Bmiga-1200/b1200-hardware/DP_USB2_KVM.kicad_sch

## KiCad design DP_USB2_KVM.kicad_sch (2026-01-02, an earlier design)

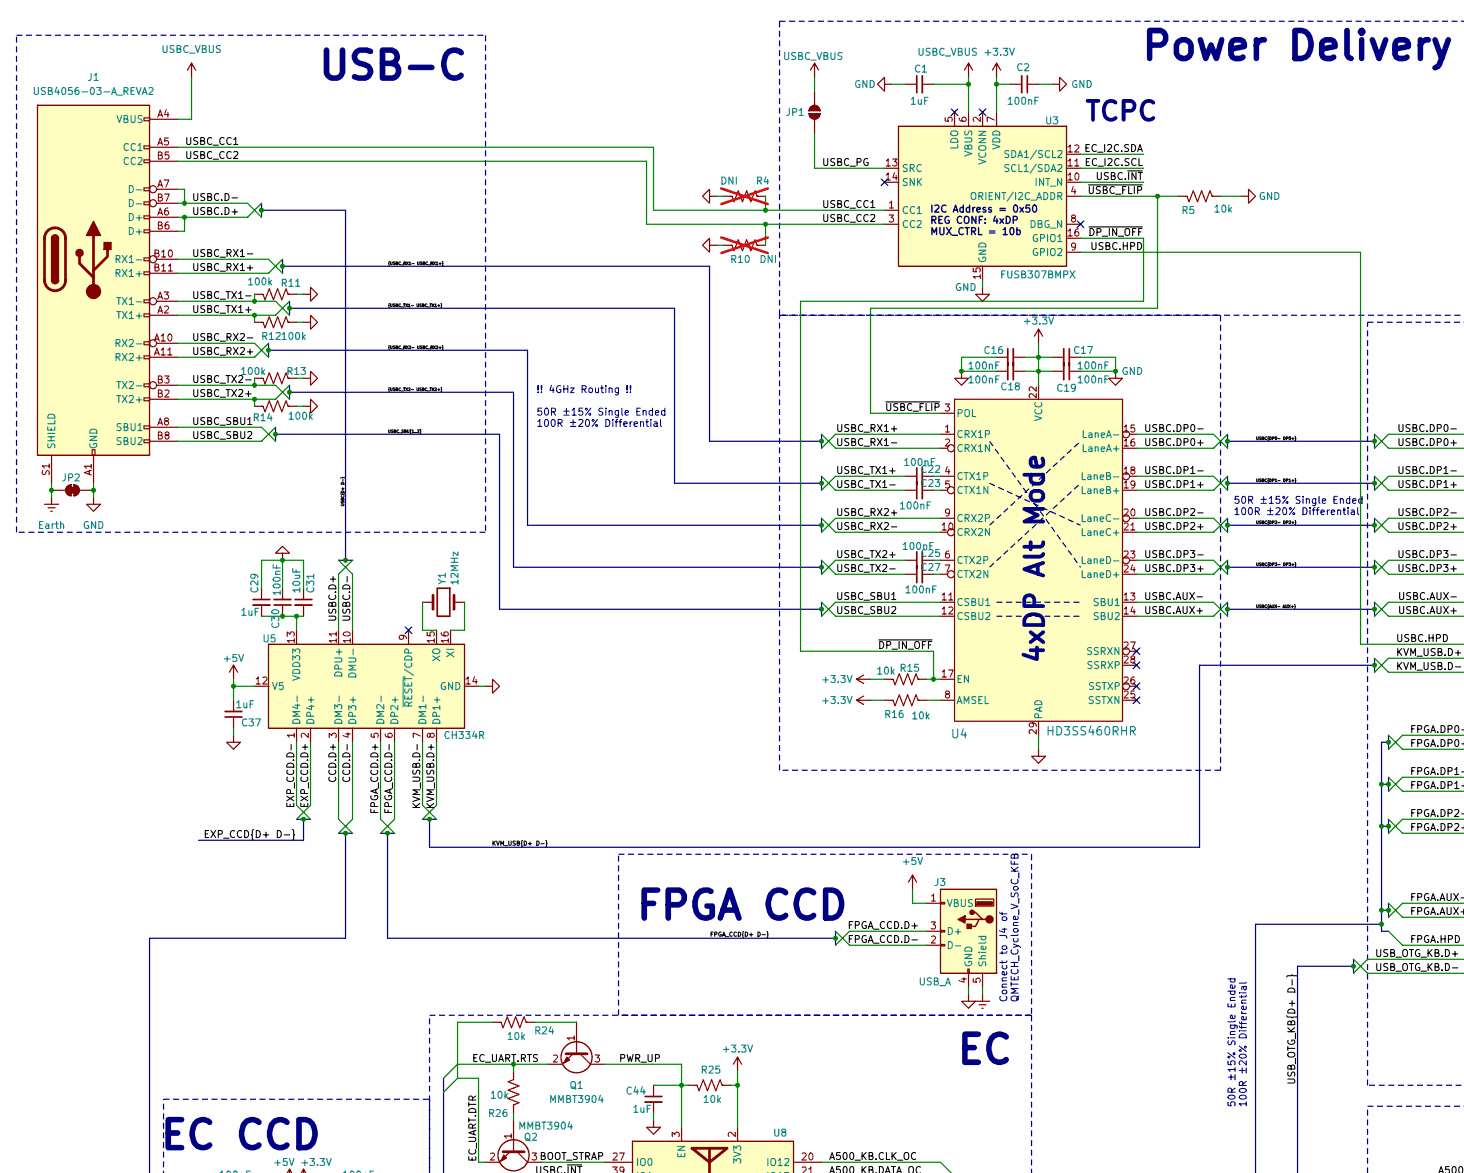
[picture p4: schematic DP_USB2_KVM.kicad_sch, part in row 1, column 1]

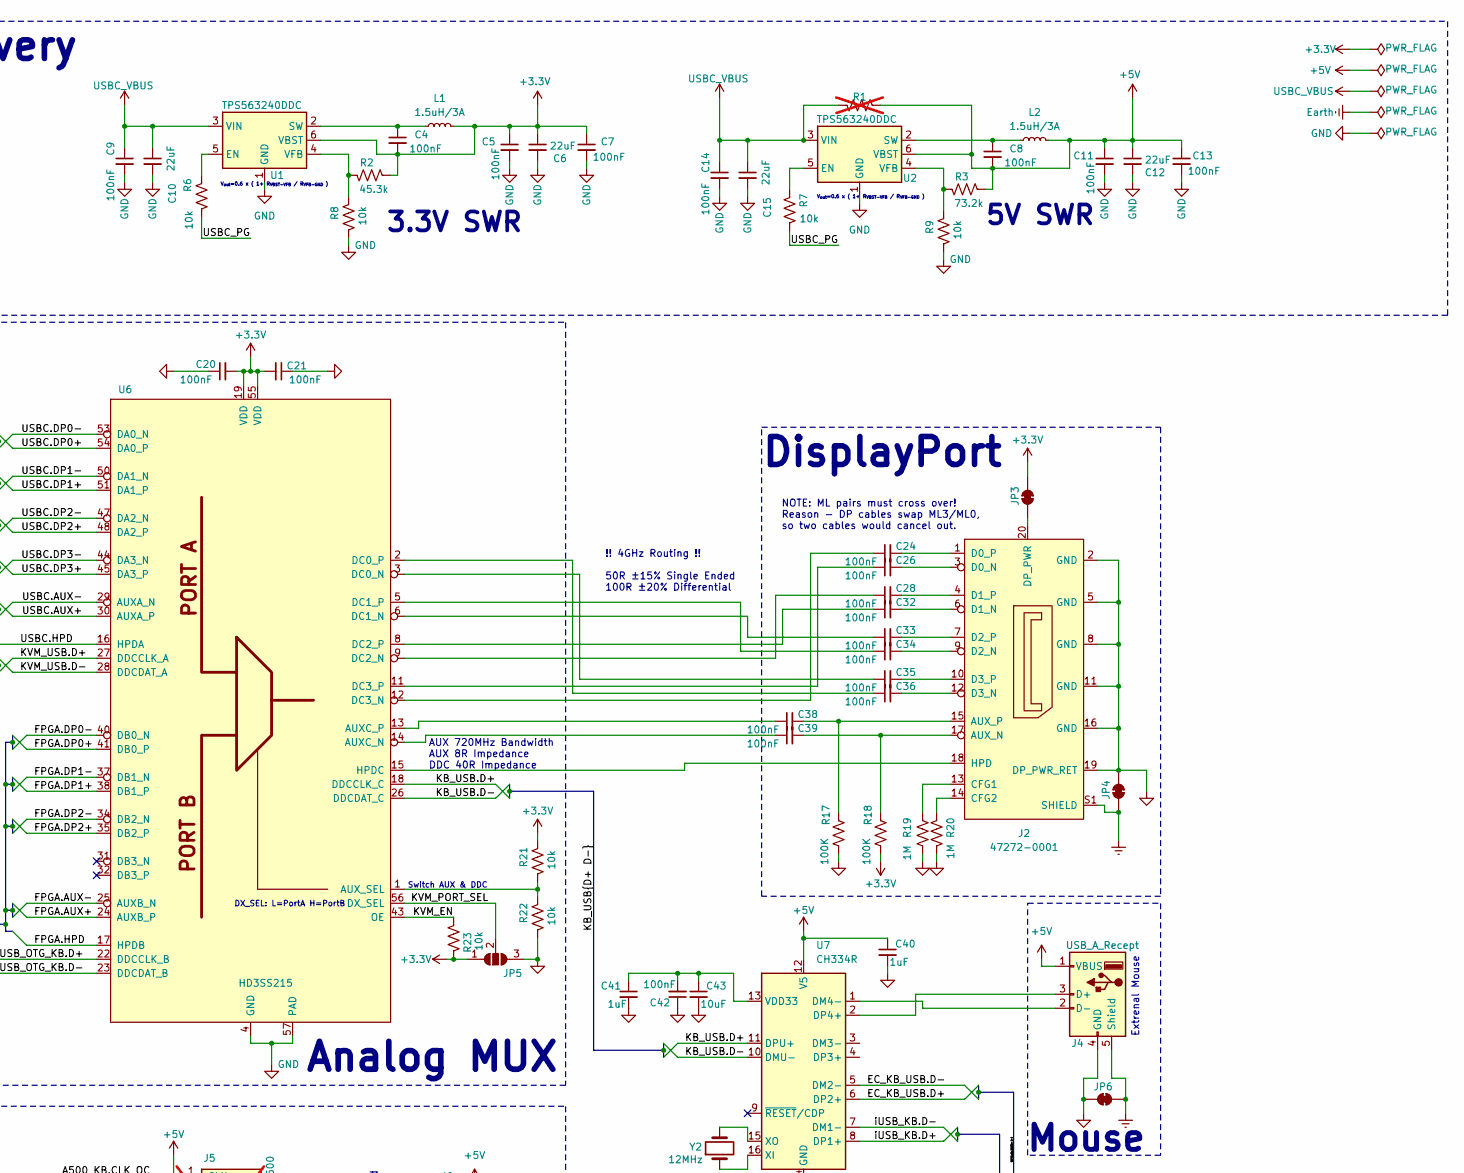
[picture p5: schematic DP_USB2_KVM.kicad_sch, part in row 1, column 2]

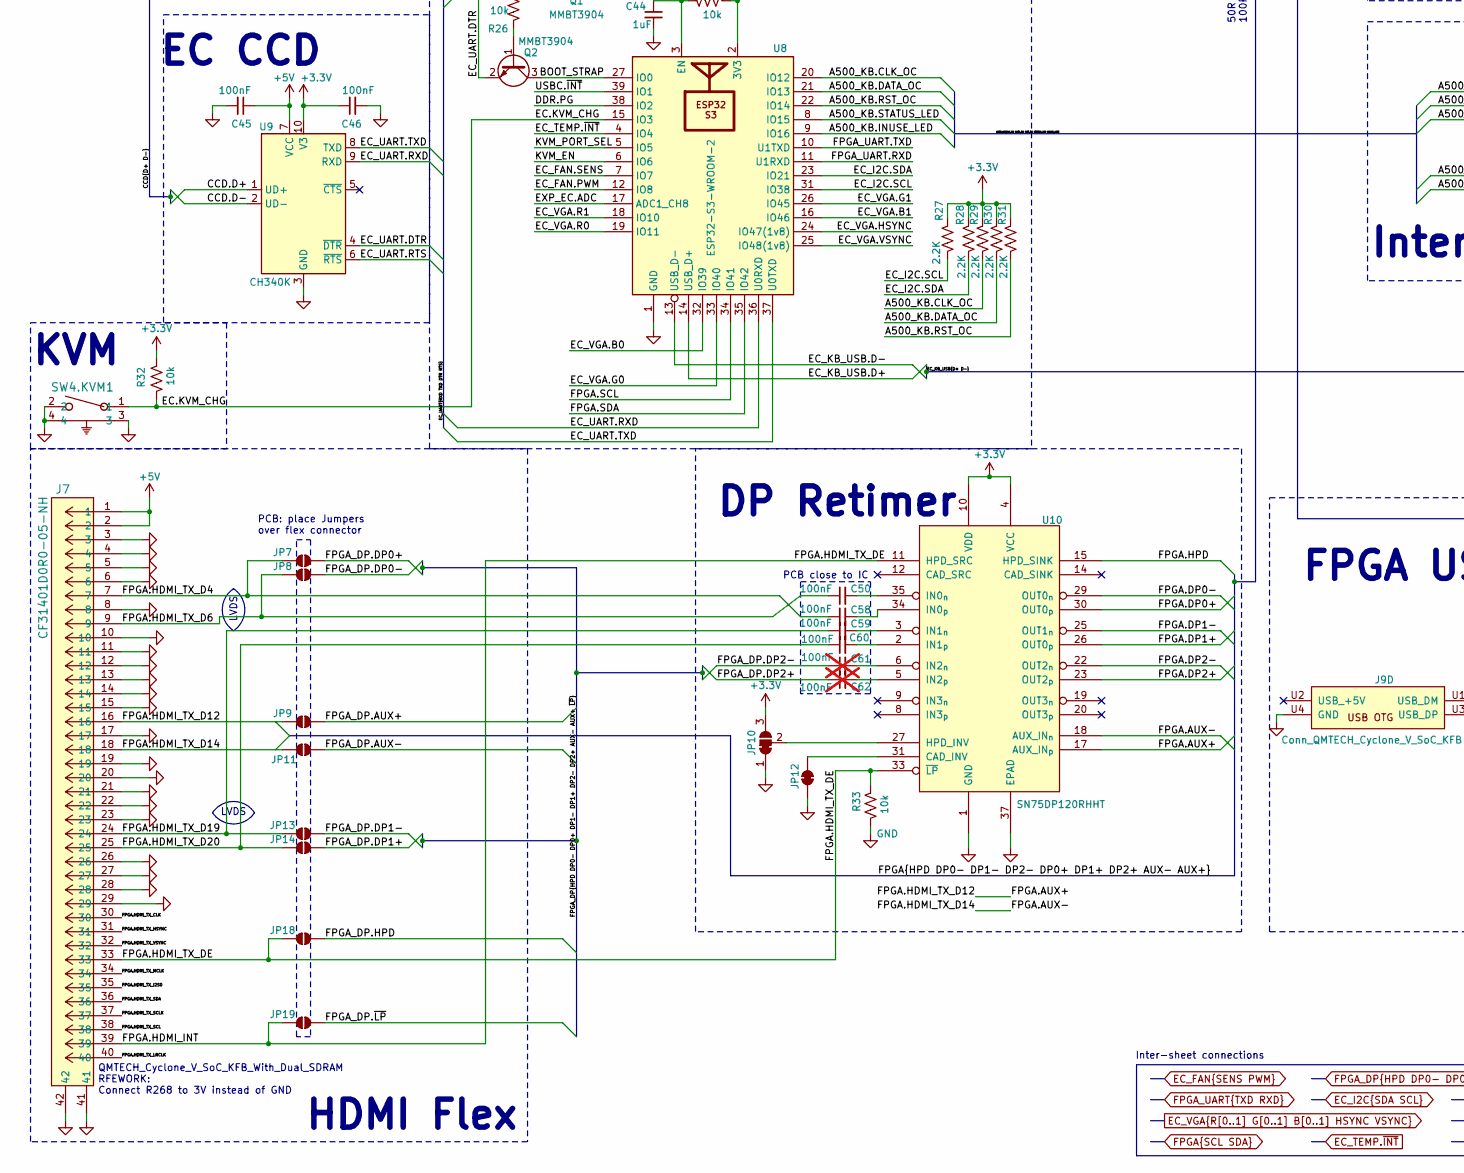
[picture p6: schematic DP_USB2_KVM.kicad_sch, part in row 2, column 1]

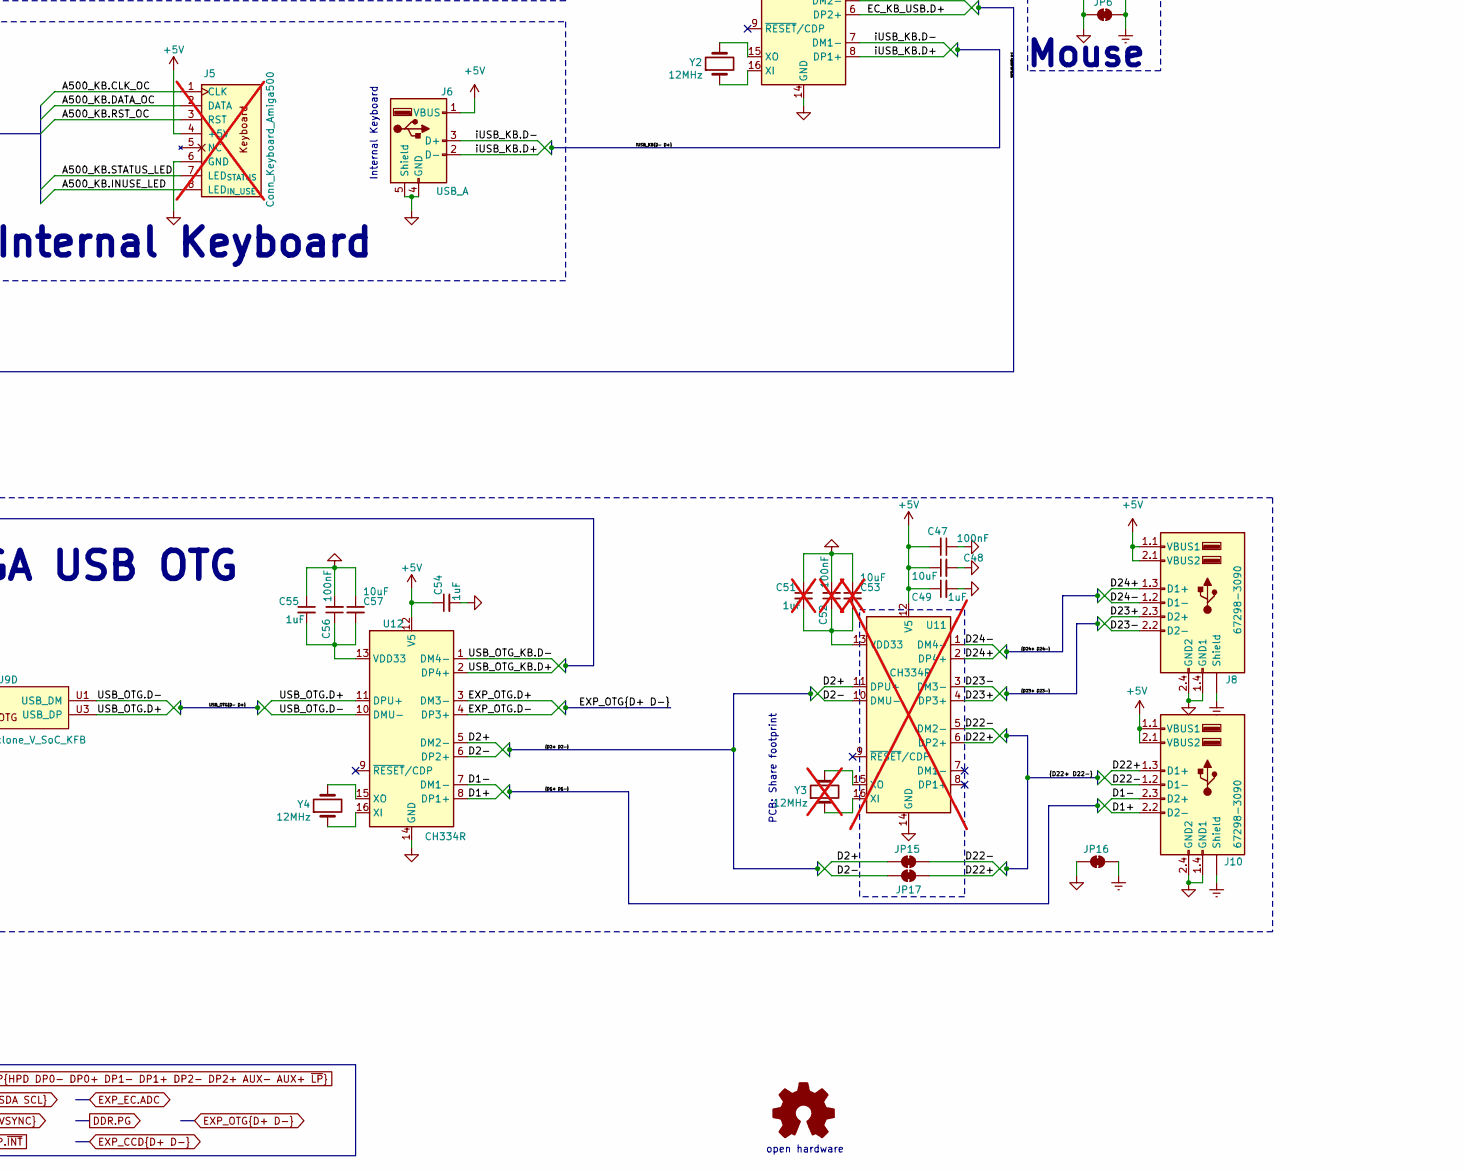
[picture p7: schematic DP_USB2_KVM.kicad_sch, part in row 2, column 2]

Parts:
C1: 1uF; C_0603_1608Metric_Pad1.08x0.95mm_HandSolder
C2, C4, C5, C8, C9, C11, C14, C16, C17, C18, C19, C20, C21, C22, C23, C24, C25, C26, C27, C28, C32, C33, C34, C35, C36, C38, C39, C50, C58, C59, C60: 100nF; C_0603_1608Metric_Pad1.08x0.95mm_HandSolder
C6, C10, C12, C15: 22uF; C_0603_1608Metric_Pad1.08x0.95mm_HandSolder
C7, C13: 100nF; C_1210_3225Metric_Pad1.33x2.70mm_HandSolder
C29, C37, C40, C41, C44, C49, C54, C55: 1uF; C_0805_2012Metric_Pad1.18x1.45mm_HandSolder
C30, C42, C45, C46, C47, C56: 100nF; C_0805_2012Metric_Pad1.18x1.45mm_HandSolder
C31, C43, C48, C57: 10uF; C_0805_2012Metric_Pad1.18x1.45mm_HandSolder
C51: 1uF; C_0805_2012Metric_Pad1.18x1.45mm_HandSolder; not fitted
C52: 100nF; C_0805_2012Metric_Pad1.18x1.45mm_HandSolder; not fitted
C53: 10uF; C_0805_2012Metric_Pad1.18x1.45mm_HandSolder; not fitted
C61, C62: 100nF; C_0603_1608Metric_Pad1.08x0.95mm_HandSolder; not fitted
J1: USB4056-03-A_REVA2; GCT_USB4056-03-A_REVA2; PARTREV A2
J2: 47272-0001; MOLEX_47272-0001
J3, J6: USB_A; USB_A_Molex_105057_Vertical
J4: USB_A_Recept; USB_A_Molex_67643_Horizontal
J5: Conn_Keyboard_Amiga500; PinHeader_1x08_P2.54mm_Vertical; not fitted
J7: CF31401D0R0-05-NH; CONN40_CF3140_CVI
J8, J10: 67298-3090; USB_MOLEX_8PIN_RA
J9: Conn_QMTECH_Cyclone_V_SoC_KFB; PinSocket_QMTECH_Cyclone_V_KFN_2x20_P2.54mm_Vertical
JP1, JP7, JP8, JP9, JP11, JP13, JP14, JP18, JP19: SolderJumper_2_Open; SolderJumper-2_P1.3mm_Open_Pad1.0x1.5mm
JP2, JP3, JP4, JP6, JP12, JP15, JP16, JP17: SolderJumper_2_Bridged; SolderJumper-2_P1.3mm_Bridged_Pad1.0x1.5mm
JP5: SolderJumper_3_Open; SolderJumper-3_P1.3mm_Open_Pad1.0x1.5mm
JP10: SolderJumper_3_Bridged12; SolderJumper-3_P1.3mm_Bridged12_Pad1.0x1.5mm
L1, L2: 1.5uH/3A; L_1008_2520Metric_Pad1.43x2.20mm_HandSolder
Q1, Q2: MMBT3904; SOT-23_Handsoldering
R1, R4, R10: DNI; R_0603_1608Metric_Pad0.98x0.95mm_HandSolder; not fitted
R2: 45.3k; R_0603_1608Metric_Pad0.98x0.95mm_HandSolder
R3: 73.2k; R_0603_1608Metric_Pad0.98x0.95mm_HandSolder
R5, R6, R7, R8, R9, R15, R16, R21, R22, R23, R24, R25, R26, R32, R33: 10k; R_0603_1608Metric_Pad0.98x0.95mm_HandSolder
R11, R12, R13, R14: 100k; R_0603_1608Metric_Pad0.98x0.95mm_HandSolder
R17, R18: 100K; R_0603_1608Metric_Pad0.98x0.95mm_HandSolder
R19, R20: 1M; R_0603_1608Metric_Pad0.98x0.95mm_HandSolder
R27, R28, R29, R30, R31: 2.2K; R_0603_1608Metric_Pad0.98x0.95mm_HandSolder
SW4.KVM1: 1-1825027-1; SW2_1825027-A_TEC
U1, U2: TPS563240DDC; SOT-23-6_Handsoldering
U3: FUSB307BMPX; WQFN-16-1EP_3x3mm_P0.5mm_EP1.75x1.75mm_ThermalVias
U4: HD3SS460RHR; RHR0028A
U5, U7, U12: CH334R; QSOP-16_3.9x4.9mm_P0.635mm
U6: HD3SS215; VQFN-56_EP_7.8x7.8_Pitch0.5mm
U8: ESP32-S3-WROOM-2
U9: CH340K; SSOP-10-1EP_3.9x4.9mm_P1mm_EP2.1x3.3mm
U10: SN75DP120RHHT; QFN50P600X600X100-37N; MPN SN75DP120RHHT
U11: CH334R; QSOP-16_3.9x4.9mm_P0.635mm; not fitted
Y1, Y2, Y4: 12MHz; Crystal_HC49-U_Horizontal
Y3: 12MHz; Crystal_HC49-U_Horizontal; not fitted

Connections:
+3.3V: C2.2, C4.2, C5.1, C6.1, C7.1, C16.2, C17.2, C18.2, C19.2, C20.2, C21.2, C46.1, JP3.1 (A), JP5.1 (A), JP10.3 (B), L1.2, R2.1, R15.2, R16.2, R18.2, R21.2, R23.2, R25.1, R27.2, R28.2, R29.2, R30.2, R31.2, R32.1, U1.6 (VBST), U3.7 (VDD), U4.22 (VCC), U6.19 (VDD), U6.55 (VDD), U8.2 (3V3), U9.10 (V3), U10.4 (VCC), U10.10 (VDD), U10.16 (VCC), U10.24 (VCC), U10.28 (VCC), U10.36 (VCC)
+5V: C8.2, C11.1, C12.1, C13.1, C37.2, C40.1, C45.1, C47.2, C48.1, C49.1, C54.1, J3.1 (VBUS), J4.1 (VBUS), J5.4 (+5V), J6.1 (VBUS), J7.1, J7.2, J8.1.1 (VBUS1), J8.2.1 (VBUS2), J10.1.1 (VBUS1), J10.2.1 (VBUS2), L2.2, R1.1, R3.1, U2.6 (VBST), U5.12 (V5), U7.12 (V5), U9.7 (VCC), U11.12 (V5), U12.12 (V5)
A500_KB.CLK_OC: J5.1 (CLK), R29.1, U8.20 (IO12)
A500_KB.DATA_OC: J5.2 (DATA), R30.1, U8.21 (IO13)
A500_KB.INUSE_LED: J5.8 (LED_{IN_USE}), U8.9 (IO16)
A500_KB.RST_OC: J5.3 (RST), R31.1, U8.22 (IO14)
A500_KB.STATUS_LED: J5.7 (LED_{STATUS}), U8.8 (IO15)
BOOT_STRAP: Q2.3 (C), U8.27 (IO0)
CCD.D+: U5.3 (DM3-), U9.1 (UD+)
CCD.D-: U5.4 (DP3+), U9.2 (UD-)
D1+: J10.2.2 (D2-), U12.8 (DP1+)
D1-: J10.2.3 (D2+), U12.7 (DM1-)
D2+: JP15.1 (A), U11.11 (DPU+), U12.5 (DM2-)
D2-: JP17.1 (A), U11.10 (DMU-), U12.6 (DP2+)
D22+: J10.1.3 (D1+), JP17.2 (B), U11.6 (DP2+)
D22-: J10.1.2 (D1-), JP15.2 (B), U11.5 (DM2-)
D23+: J8.2.3 (D2+), U11.4 (DP3+)
D23-: J8.2.2 (D2-), U11.3 (DM3-)
D24+: J8.1.3 (D1+), U11.2 (DP4+)
D24-: J8.1.2 (D1-), U11.1 (DM4-)
DDR.PG: U8.38 (IO2)
EC.KVM_CHG: R32.2, SW4.KVM1.1, U8.15 (IO3)
EC_FAN.PWM: U8.12 (IO8)
EC_FAN.SENS: U8.7 (IO7)
EC_I2C.SCL: R27.1, U3.11 (SCL1/SDA2), U8.31 (IO38)
EC_I2C.SDA: R28.1, U3.12 (SDA1/SCL2), U8.23 (IO21)
EC_KB_USB.D+: U7.6 (DP2+), U8.14 (USB_D+)
EC_KB_USB.D-: U7.5 (DM2-), U8.13 (USB_D-)
EC_TEMP.~INT: U8.4 (IO4)
EC_UART.DTR: Q1.2 (E), Q2.2 (E), R24.2, R26.2, U9.4 (~DTR), U9.6 (~RTS)
EC_UART.RXD: U8.36 (U0RXD), U9.9 (RXD)
EC_UART.TXD: U8.37 (U0TXD), U9.8 (TXD)
EC_VGA.B0: U8.32 (MTCK)
EC_VGA.B1: U8.16 (IO46)
EC_VGA.G0: U8.33 (MTDO)
EC_VGA.G1: U8.26 (IO45)
EC_VGA.HSYNC: U8.24 (IO47(1v8))
EC_VGA.R0: U8.19 (IO11)
EC_VGA.R1: U8.18 (IO10)
EC_VGA.VSYNC: U8.25 (IO48(1v8))
EXP_CCD.D+: U5.2 (DP4+)
EXP_CCD.D-: U5.1 (DM4-)
EXP_EC.ADC: U8.17 (IO9)
EXP_OTG.D+: U12.3 (DM3-)
EXP_OTG.D-: U12.4 (DP3+)
Earth: J1.S1 (SHIELD), J1.S2 (SHIELD), J1.S3 (SHIELD), J1.S4 (SHIELD), J2.S1 (SHIELD), J2.S2 (SHIELD), J2.S3 (SHIELD), J2.S4 (SHIELD), J3.5 (Shield), J4.5 (Shield), J8.GND@3 (Shield), J8.GND@4 (Shield), J8.GND@5 (Shield), J8.GND@6 (Shield), J10.GND@3 (Shield), J10.GND@4 (Shield), J10.GND@5 (Shield), J10.GND@6 (Shield), JP2.1 (A), JP4.2 (B), JP6.2 (B), JP16.2 (B)
FPGA.AUX+: J7.16, JP9.2 (B), U6.24 (AUXB_P), U10.17 (AUX_IN_{p})
FPGA.AUX-: J7.18, JP11.2 (B), U6.25 (AUXB_N), U10.18 (AUX_IN_{n})
FPGA.DP0+: U6.41 (DB0_P), U10.30 (OUT0_{p})
FPGA.DP0-: U6.40 (DB0_N), U10.29 (OUT0_{n})
FPGA.DP1+: U6.38 (DB1_P), U10.26 (OUT0_{p})
FPGA.DP1-: U6.37 (DB1_N), U10.25 (OUT1_{n})
FPGA.DP2+: U6.35 (DB2_P), U10.23 (OUT2_{p})
FPGA.DP2-: U6.34 (DB2_N), U10.22 (OUT2_{n})
FPGA.HDMI_INT: J7.33, J7.39, JP18.2 (B), JP19.2 (B), R33.2, U10.11 (HPD_SRC), U10.33 (~LP)
FPGA.HDMI_TX_CLK: J7.30
FPGA.HDMI_TX_D4: C58.1, J7.7, JP7.2 (B)
FPGA.HDMI_TX_D6: C50.1, J7.9, JP8.2 (B)
FPGA.HDMI_TX_D19: C59.1, J7.24, JP13.2 (B)
FPGA.HDMI_TX_D20: C60.1, J7.25, JP14.2 (B)
FPGA.HDMI_TX_HSYNC: J7.31
FPGA.HDMI_TX_I2S0: J7.35
FPGA.HDMI_TX_LRCLK: J7.40
FPGA.HDMI_TX_MCLK: J7.34
FPGA.HDMI_TX_SCL: J7.38
FPGA.HDMI_TX_SCLK: J7.37
FPGA.HDMI_TX_SDA: J7.36
FPGA.HDMI_TX_VSYNC: J7.32
FPGA.HPD: U6.17 (HPDB), U10.15 (HPD_SINK)
FPGA.SCL: U8.34 (MTDI)
FPGA.SDA: U8.35 (MTMS)
FPGA_CCD.D+: J3.3 (D+), U5.5 (DM2-)
FPGA_CCD.D-: J3.2 (D-), U5.6 (DP2+)
FPGA_DP.AUX+: JP9.1 (A)
FPGA_DP.AUX-: JP11.1 (A)
FPGA_DP.DP0+: JP7.1 (A)
FPGA_DP.DP0-: JP8.1 (A)
FPGA_DP.DP1+: JP14.1 (A)
FPGA_DP.DP1-: JP13.1 (A)
FPGA_DP.DP2+: C62.1
FPGA_DP.DP2-: C61.1
FPGA_DP.HPD: JP18.1 (A)
FPGA_DP.~LP: JP19.1 (A)
FPGA_UART.RXD: U8.11 (IO18)
FPGA_UART.TXD: U8.10 (IO17)
GND: C1.1, C2.1, C5.2, C6.2, C7.2, C9.2, C10.2, C11.2, C12.2, C13.2, C14.2, C15.2, C16.1, C17.1, C18.1, C19.1, C20.1, C21.1, C29.1, C30.2, C31.1, C37.1, C40.2, C41.2, C42.1, C43.2, C44.2, C45.2, C46.2, C47.1, C48.2, C49.2, C51.1, C52.2, C53.1, C54.2, C55.1, C56.2, C57.1, J1.A1 (GND), J1.A12 (GND), J1.B1 (GND), J1.B12 (GND), J2.2 (GND), J2.5 (GND), J2.8 (GND), J2.11 (GND), J2.16 (GND), J2.19 (DP_PWR_RET), J3.4 (GND), J4.4 (GND), J5.6 (GND), J6.4 (GND), J6.5 (Shield), J7.3, J7.4, J7.5, J7.6, J7.8, J7.10, J7.11, J7.12, J7.13, J7.14, J7.15, J7.17, J7.19, J7.20, J7.21, J7.22, J7.23, J7.26, J7.27, J7.28, J7.29, J7.41, J7.42, J8.1.4 (GND1), J8.2.4 (GND2), J9.U4 (GND), J10.1.4 (GND1), J10.2.4 (GND2), JP2.2 (B), JP4.1 (A), JP5.3 (B), JP6.1 (A), JP10.1 (A), JP12.2 (B), JP16.1 (A), R4.1, R5.1, R8.1, R9.1, R10.1, R11.2, R12.2, R13.2, R14.2, R17.2, R19.2, R20.2, R22.1, R33.1, SW4.KVM1.2, SW4.KVM1.3, SW4.KVM1.4, U1.1 (GND), U2.1 (GND), U3.15 (GND), U3.17 (GND), U4.29 (PAD), U5.14 (GND), U6.4 (GND), U6.7 (GND), U6.10 (GND), U6.33 (GND), U6.36 (GND), U6.39 (GND), U6.46 (GND), U6.49 (GND), U6.52 (GND), U6.57 (PAD), U7.14 (GND), U8.1 (GND), U8.40 (GND), U8.41 (GND), U9.3 (GND), U9.11 (GND), U10.1 (GND), U10.7 (GND), U10.13 (GND), U10.21 (GND), U10.32 (GND), U10.37 (EPAD), U11.14 (GND), U12.14 (GND)
KB_USB.D+: U6.18 (DDCCLK_C), U7.11 (DPU+)
KB_USB.D-: U6.26 (DDCDAT_C), U7.10 (DMU-)
KVM_EN: R23.1, U6.43 (OE), U8.6 (IO6)
KVM_PORT_SEL: JP5.2 (C), U6.56 (DX_SEL), U8.5 (IO5)
KVM_USB.D+: U5.8 (DP1+), U6.27 (DDCCLK_A)
KVM_USB.D-: U5.7 (DM1-), U6.28 (DDCDAT_A)
unnamed: C4.1, L1.1, U1.2 (SW)
unnamed: C8.1, L2.1, U2.2 (SW)
unnamed: C22.2, U4.4 (CTX1P)
unnamed: C23.2, U4.5 (CTX1N)
unnamed: C24.1, U6.12 (DC3_N)
unnamed: C24.2, J2.1 (D0_P)
unnamed: C25.2, U4.6 (CTX2P)
unnamed: C26.1, U6.11 (DC3_P)
unnamed: C26.2, J2.3 (D0_N)
unnamed: C27.2, U4.7 (CTX2N)
unnamed: C28.1, U6.9 (DC2_N)
unnamed: C28.2, J2.4 (D1_P)
unnamed: C29.2, C30.1, C31.2, U5.13 (VDD33)
unnamed: C32.1, U6.8 (DC2_P)
unnamed: C32.2, J2.6 (D1_N)
unnamed: C33.1, U6.6 (DC1_N)
unnamed: C33.2, J2.7 (D2_P)
unnamed: C34.1, U6.5 (DC1_P)
unnamed: C34.2, J2.9 (D2_N)
unnamed: C35.1, U6.3 (DC0_N)
unnamed: C35.2, J2.10 (D3_P)
unnamed: C36.1, U6.2 (DC0_P)
unnamed: C36.2, J2.12 (D3_N)
unnamed: C38.1, U6.13 (AUXC_P)
unnamed: C38.2, J2.15 (AUX_P), R17.1
unnamed: C39.1, U6.14 (AUXC_N)
unnamed: C39.2, J2.17 (AUX_N), R18.1
unnamed: C41.1, C42.2, C43.1, U7.13 (VDD33)
unnamed: C50.2, U10.35 (IN0_{n})
unnamed: C51.2, C52.1, C53.2, U11.13 (VDD33)
unnamed: C55.2, C56.1, C57.2, U12.13 (VDD33)
unnamed: C58.2, U10.34 (IN0_{p})
unnamed: C59.2, U10.3 (IN1_{n})
unnamed: C60.2, U10.2 (IN1_{p})
unnamed: C61.2, U10.6 (IN2_{n})
unnamed: C62.2, U10.5 (IN2_{p})
unnamed: J2.13 (CFG1), R19.1
unnamed: J2.14 (CFG2), R20.1
unnamed: J2.18 (HPD), U6.15 (HPDC)
unnamed: J2.20 (DP_PWR), JP3.2 (B)
unnamed: J4.2 (D-), U7.1 (DM4-)
unnamed: J4.3 (D+), U7.2 (DP4+)
unnamed: JP10.2 (C), U10.27 (HPD_INV)
unnamed: JP12.1 (A), U10.31 (CAD_INV)
unnamed: Q1.1 (B), R24.1
unnamed: Q2.1 (B), R26.1
unnamed: R2.2, R8.2, U1.4 (VFB)
unnamed: R3.2, R9.2, U2.4 (VFB)
unnamed: R6.2, U1.5 (EN)
unnamed: R7.2, U2.5 (EN)
unnamed: R16.1, U4.8 (AMSEL)
unnamed: R21.1, R22.2, U6.1 (AUX_SEL)
unnamed: U5.15 (XO), Y1.2
unnamed: U5.16 (XI), Y1.1
unnamed: U7.15 (XO), Y2.2
unnamed: U7.16 (XI), Y2.1
unnamed: U8.28 (NC), U8.29 (NC), U8.30 (NC)
unnamed: U11.15 (XO), Y3.2
unnamed: U11.16 (XI), Y3.1
unnamed: U12.15 (XO), Y4.2
unnamed: U12.16 (XI), Y4.1
PWR_UP: C44.1, Q1.3 (C), R25.2, U8.3 (EN)
USBC.AUX+: U4.14 (SBU2), U6.30 (AUXA_P)
USBC.AUX-: U4.13 (SBU1), U6.29 (AUXA_N)
USBC.D+: J1.A6 (D+), J1.B6 (D+), U5.11 (DPU+)
USBC.D-: J1.A7 (D-), J1.B7 (D-), U5.10 (DMU-)
USBC.DP0+: U4.16 (LaneA+), U6.54 (DA0_P)
USBC.DP0-: U4.15 (LaneA-), U6.53 (DA0_N)
USBC.DP1+: U4.19 (LaneB+), U6.51 (DA1_P)
USBC.DP1-: U4.18 (LaneB-), U6.50 (DA1_N)
USBC.DP2+: U4.21 (LaneC+), U6.48 (DA2_P)
USBC.DP2-: U4.20 (LaneC-), U6.47 (DA2_N)
USBC.DP3+: U4.24 (LaneD+), U6.45 (DA3_P)
USBC.DP3-: U4.23 (LaneD-), U6.44 (DA3_N)
USBC.HPD: R15.1, U3.9 (GPIO2), U3.16 (GPIO1), U4.17 (EN), U6.16 (HPDA)
USBC.~INT: U3.10 (INT_N), U8.39 (IO1)
USBC_CC1: J1.A5 (CC1), R4.2, U3.1 (CC1)
USBC_CC2: J1.B5 (CC2), R10.2, U3.3 (CC2)
USBC_PG: JP1.1 (A), R6.1, R7.1, U3.13 (SRC)
USBC_RX1+: J1.B11 (RX1+), U4.1 (CRX1P)
USBC_RX1-: J1.B10 (RX1-), U4.2 (CRX1N)
USBC_RX2+: J1.A11 (RX2+), U4.9 (CRX2P)
USBC_RX2-: J1.A10 (RX2-), U4.10 (CRX2N)
USBC_SBU1: J1.A8 (SBU1), U4.11 (CSBU1)
USBC_SBU2: J1.B8 (SBU2), U4.12 (CSBU2)
USBC_TX1+: C22.1, J1.A2 (TX1+), R12.1
USBC_TX1-: C23.1, J1.A3 (TX1-), R11.1
USBC_TX2+: C25.1, J1.B2 (TX2+), R14.1
USBC_TX2-: C27.1, J1.B3 (TX2-), R13.1
USBC_VBUS: C1.2, C9.1, C10.1, C14.1, C15.1, J1.A4 (VBUS), J1.A9 (VBUS), J1.B4 (VBUS), J1.B9 (VBUS), JP1.2 (B), R1.2, U1.3 (VIN), U2.3 (VIN), U3.6 (VBUS)
USB_OTG.D+: J9.U3 (USB_DP), U12.11 (DPU+)
USB_OTG.D-: J9.U1 (USB_DM), U12.10 (DMU-)
USB_OTG_KB.D+: U6.22 (DDCCLK_B), U12.2 (DP4+)
USB_OTG_KB.D-: U6.23 (DDCDAT_B), U12.1 (DM4-)
iUSB_KB.D+: J6.2 (D-), U7.8 (DP1+)
iUSB_KB.D-: J6.3 (D+), U7.7 (DM1-)
~USBC_FLIP: R5.2, U3.4 (ORIENT/I2C_ADDR), U4.3 (POL)

Notes on the sheet:
PCB: Share footprint
AUX 720MHz Bandwidth AUX 8R Impedance DDC 40R Impedance
5V SWR
I2C Address = 0x50 REG CONF: 4xDP MUX_CTRL = 10b
50R ±15% Single Ended 100R ±20% Differential
LVDS
3.3V SWR
V_{out}=0.6 x ( 1+ R_{VBST-VFB} / R_{VFB-GND} )
PCB: place Jumpers over flex connector
USB-C
Extrenal Mouse
FPGA USB OTG
FPGA CCD
4xDP Alt Mode
Inter-sheet connections
Connect to J4 of QMTECH_Cyclone_V_SoC_KFB
open hardware
Mouse
TCPC
EC CCD
!! 4GHz Routing !! 50R ±15% Single Ended 100R ±20% Differential
NOTE: ML pairs must cross over! Reason - DP cables swap ML3/ML0, so two cables would cancel out.
Internal Keyboard
QMTECH_Cyclone_V_SoC_KFB_With_Dual_SDRAM RFEWORK: Connect R268 to 3V instead of GND
DisplayPort
Analog MUX
Switch AUX & DDC
HDMI Flex
Power Delivery
KVM
PCB close to IC
DP Retimer
DX_SEL: L=PortA H=PortB
