Bmiga-1200/b1200-hardware/fpga_usb_hub.kicad_sch

## KiCad design fpga_usb_hub.kicad_sch (2026-07-11, an earlier design)

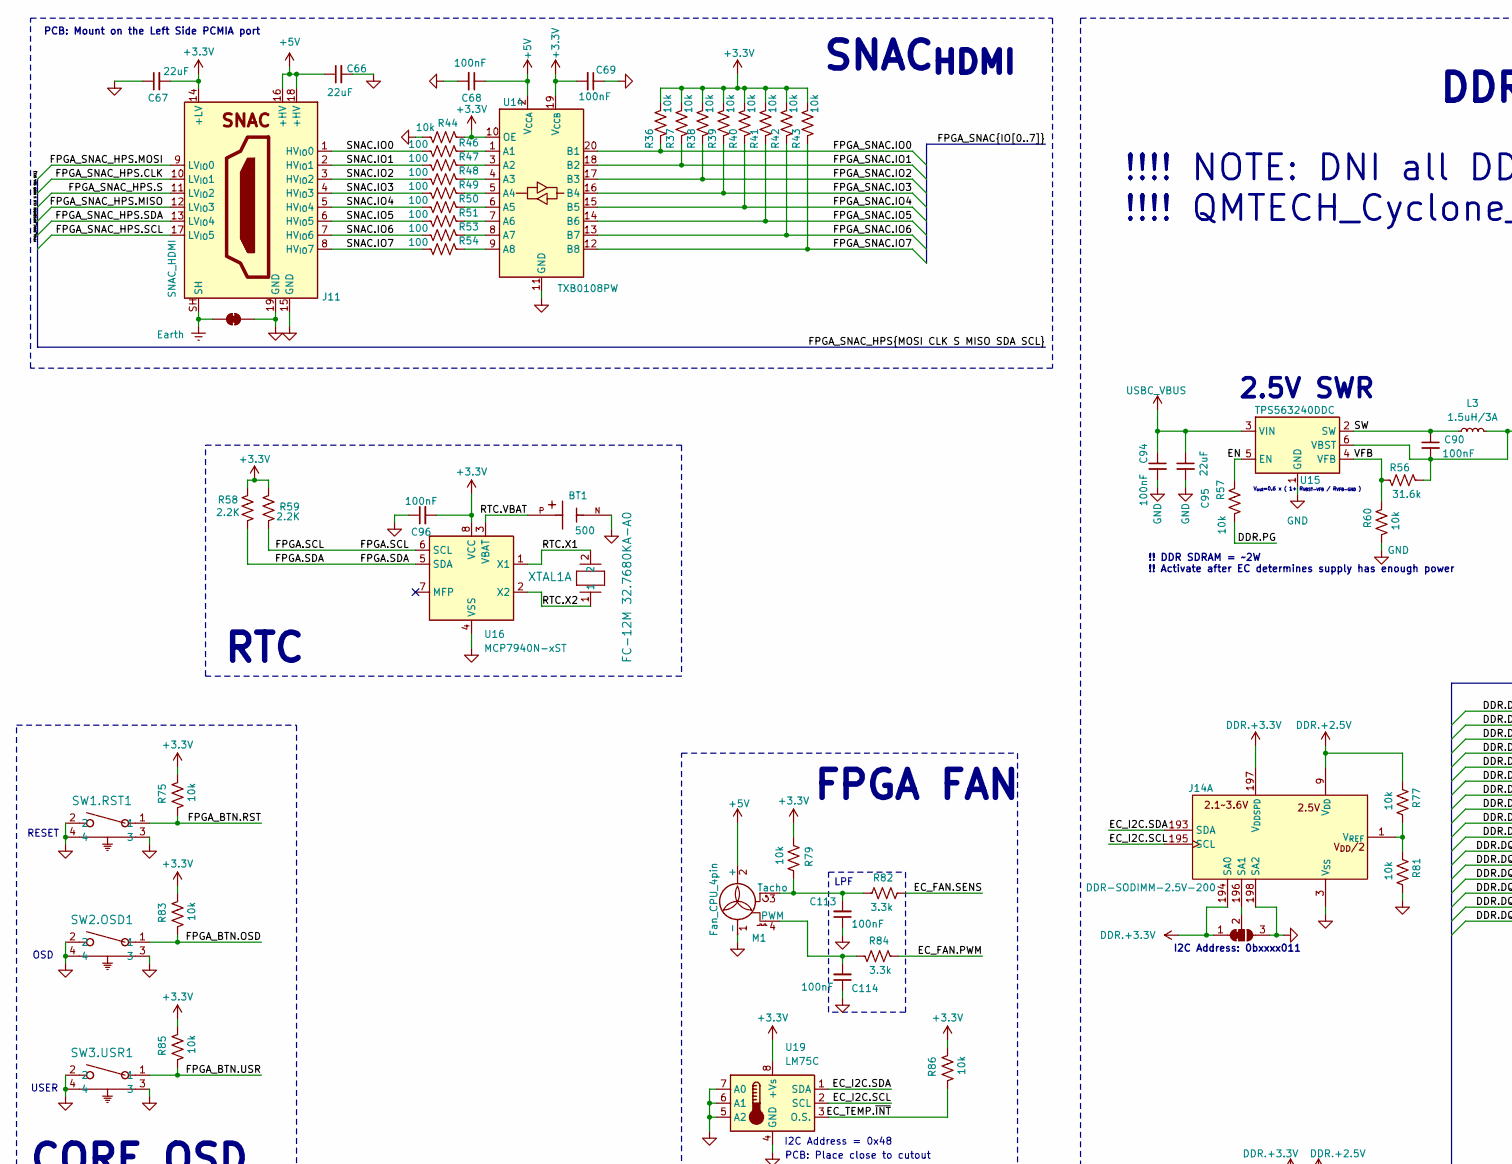
[picture p8: schematic fpga_usb_hub.kicad_sch, part in row 1, column 1]

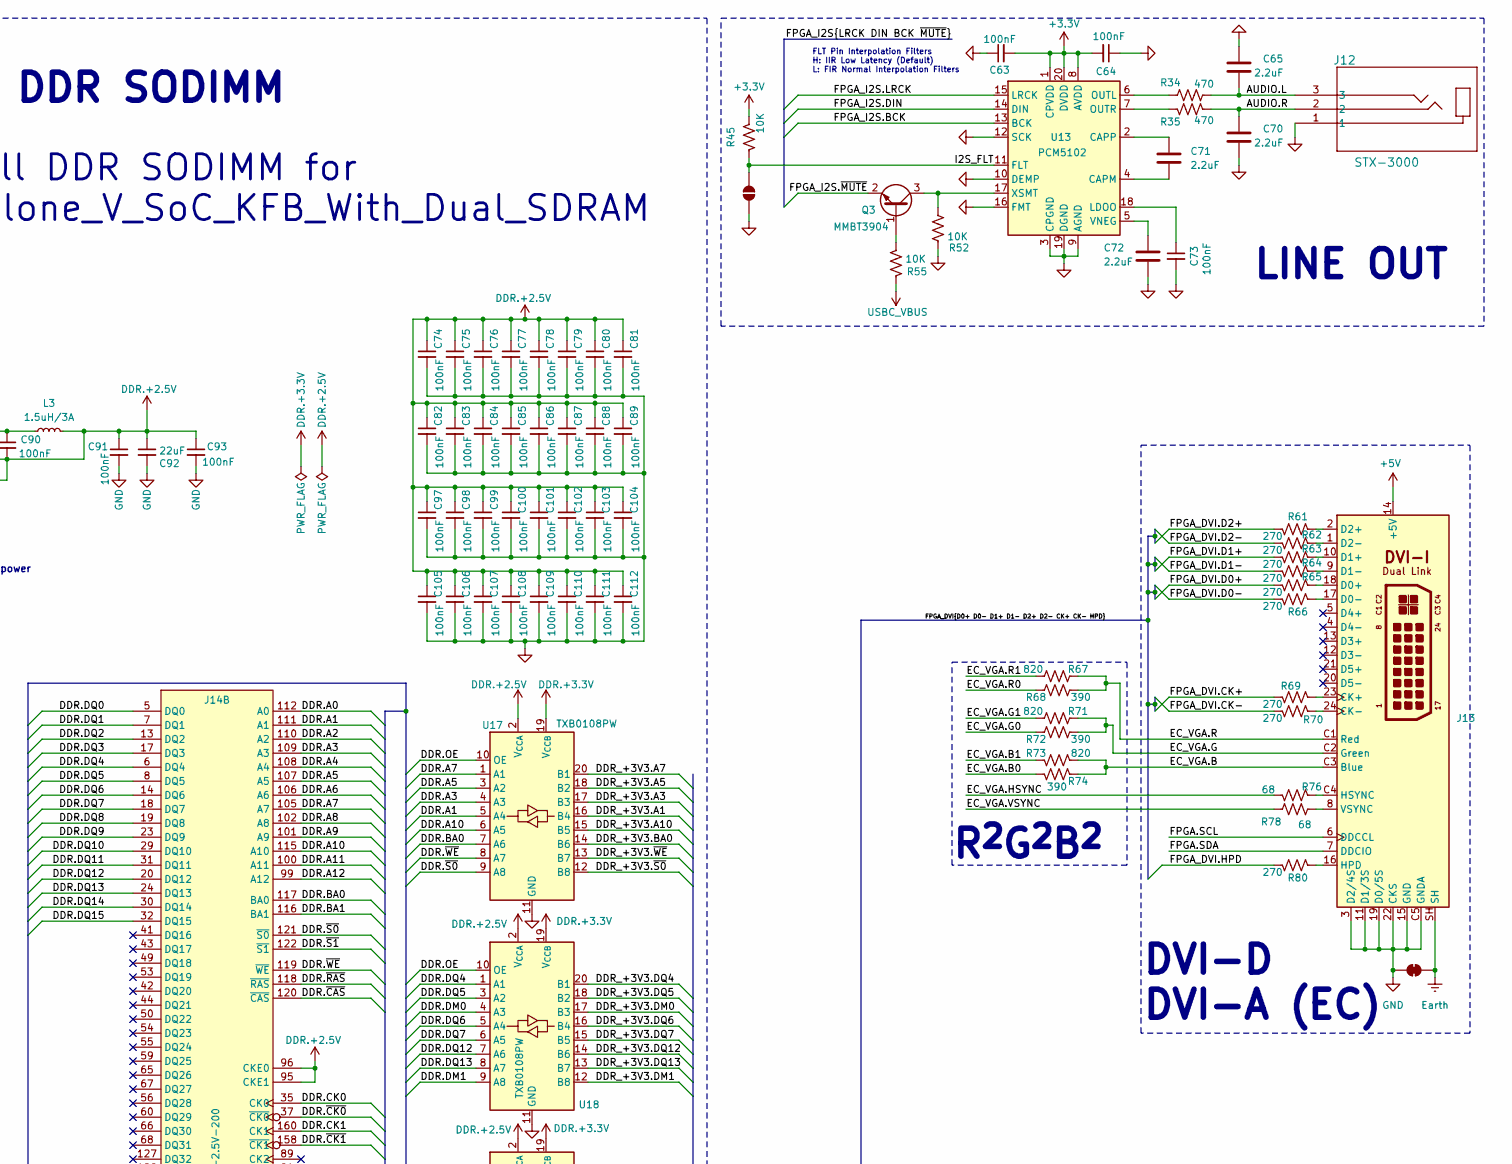
[picture p9: schematic fpga_usb_hub.kicad_sch, part in row 1, column 2]

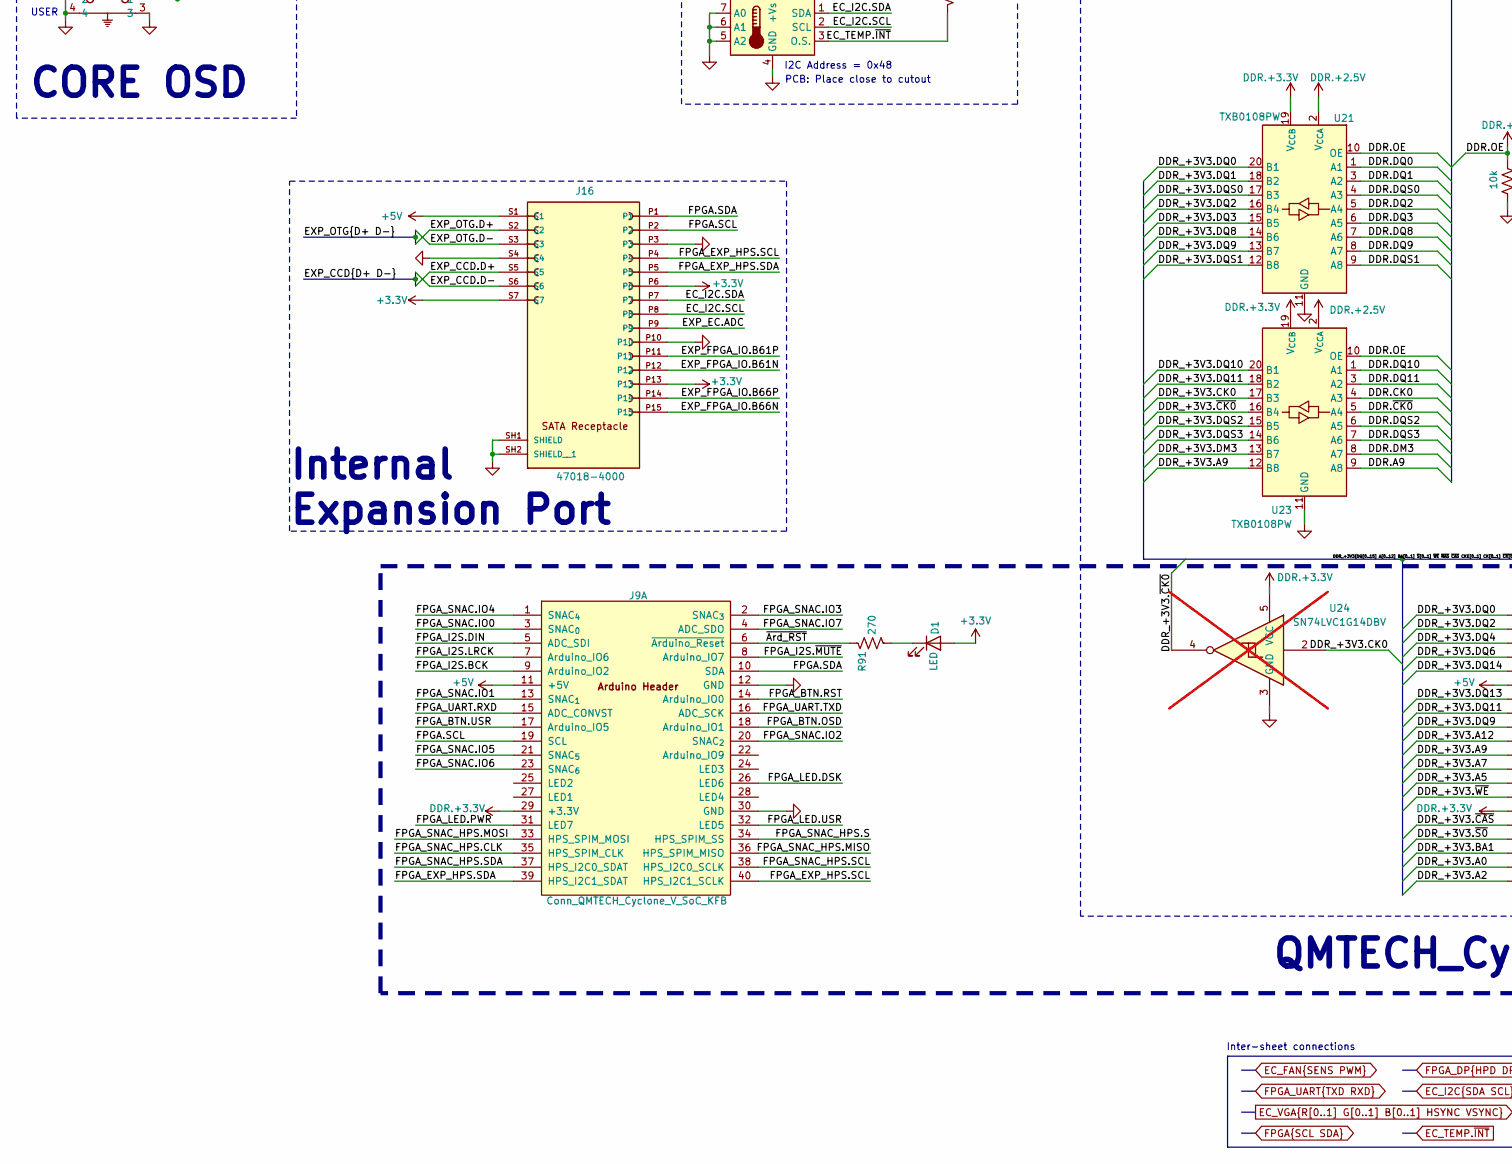
[picture p10: schematic fpga_usb_hub.kicad_sch, part in row 2, column 1]

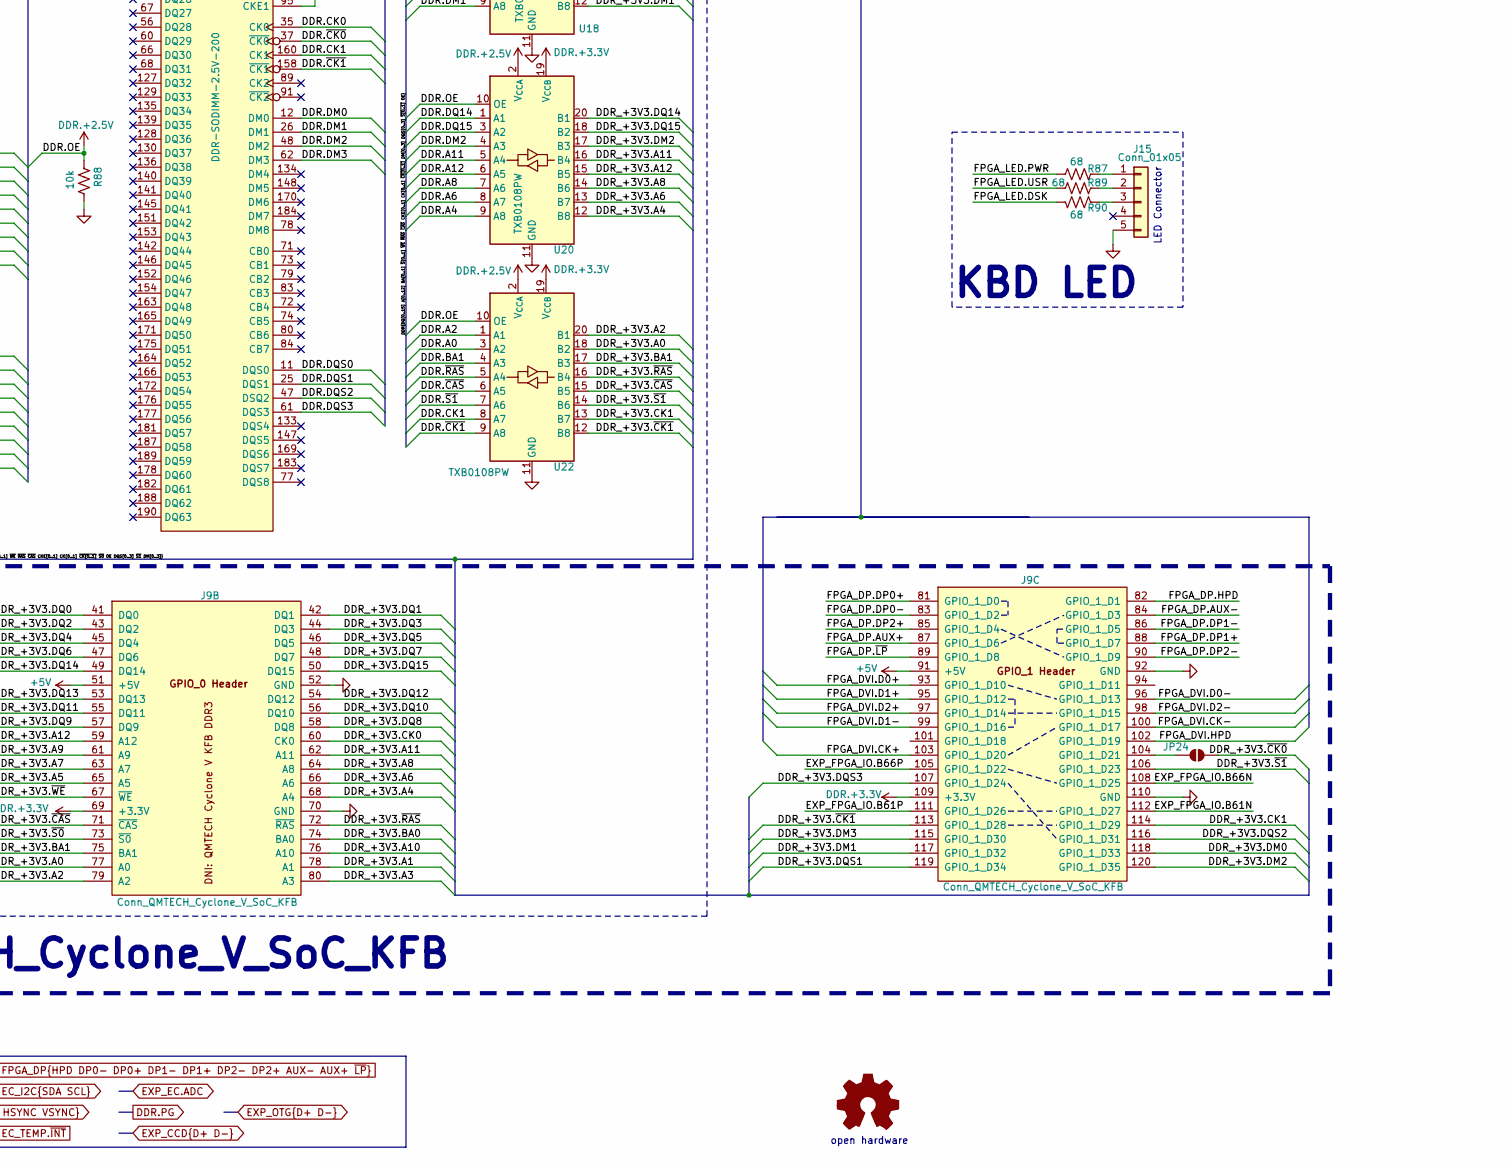
[picture p11: schematic fpga_usb_hub.kicad_sch, part in row 2, column 2]

Parts:
BT1: 500; BatteryHolder_Keystone_500; PARTREV H
C63, C64, C73, C90, C91, C94, C96, C113, C114: 100nF; C_0603_1608Metric_Pad1.08x0.95mm_HandSolder
C65, C70, C71, C72: 2.2uF; C_0805_2012Metric_Pad1.18x1.45mm_HandSolder
C66, C67, C92, C95: 22uF; C_0603_1608Metric_Pad1.08x0.95mm_HandSolder
C68, C69, C74, C75, C76, C77, C78, C79, C80, C81, C82, C83, C84, C85, C86, C87, C88, C89, C93, C97, C98, C99, C100, C101, C102, C103, C104, C105, C106, C107, C108, C109, C110, C111, C112: 100nF; C_1210_3225Metric_Pad1.33x2.70mm_HandSolder
D1: LED; LED_0805_2012Metric_Pad1.15x1.40mm_HandSolder
J9: Conn_QMTECH_Cyclone_V_SoC_KFB; PinSocket_QMTECH_Cyclone_V_KFN_2x20_P2.54mm_Vertical
J11: SNAC_HDMI; HDMI_A_Molex_208658-1001_Horizontal
J12: STX-3000; STX-3000_KYC
J13: DVI-I_Dual_Link; DVI-I_Molex_74320-1004_Horizontal
J14: DDR-SODIMM-2.5V-200; SODIMM-200_2.5V_Card_edge
J15: Conn_01x05; PinHeader_1x05_P2.54mm_Vertical
J16: 47018-4000; MOLEX_47018-4000; PARTREV M
JP20: SolderJumper_2_Open; SolderJumper-2_P1.3mm_Open_TrianglePad1.0x1.5mm
JP21, JP23: SolderJumper_2_Bridged; SolderJumper-2_P1.3mm_Bridged_Pad1.0x1.5mm
JP22: SolderJumper_3_Bridged12; SolderJumper-3_P1.3mm_Bridged12_RoundedPad1.0x1.5mm
JP24: SolderJumper_2_Open; SolderJumper-2_P1.3mm_Open_Pad1.0x1.5mm
L3: 1.5uH/3A; L_1008_2520Metric_Pad1.43x2.20mm_HandSolder
M1: Fan_CPU_4pin; FanPinHeader_1x04_P2.54mm_Vertical
Q3: MMBT3904; SOT-23
R34, R35: 470; R_0603_1608Metric_Pad0.98x0.95mm_HandSolder
R36, R37, R38, R39, R40, R41, R42, R43, R44, R57, R60, R75, R77, R79, R81, R83, R85, R86, R88: 10k; R_0603_1608Metric_Pad0.98x0.95mm_HandSolder
R45, R52, R55: 10K; R_0603_1608Metric_Pad0.98x0.95mm_HandSolder
R46, R47, R48, R49, R50, R51, R53, R54: 100; R_0603_1608Metric_Pad0.98x0.95mm_HandSolder
R56: 31.6k; R_0603_1608Metric_Pad0.98x0.95mm_HandSolder
R58, R59: 2.2K; R_0603_1608Metric_Pad0.98x0.95mm_HandSolder
R61, R62, R63, R64, R65, R66, R69, R70, R80, R91: 270; R_0603_1608Metric_Pad0.98x0.95mm_HandSolder
R67, R71, R73: 820; R_0603_1608Metric_Pad0.98x0.95mm_HandSolder
R68, R72, R74: 390; R_0603_1608Metric_Pad0.98x0.95mm_HandSolder
R76, R78, R87, R89, R90: 68; R_0603_1608Metric_Pad0.98x0.95mm_HandSolder
R82, R84: 3.3k; R_0603_1608Metric_Pad0.98x0.95mm_HandSolder
SW1.RST1, SW2.OSD1, SW3.USR1: 1-1825027-1; SW2_1825027-A_TEC
U13: PCM5102; TSSOP-20_4.4x6.5mm_P0.65mm
U14, U17, U18, U20, U21, U22, U23: TXB0108PW; TSSOP-20_4.4x6.5mm_P0.65mm
U15: TPS563240DDC; SOT-23-6_Handsoldering
U16: MCP7940N-xST; SOIC-8_3.9x4.9mm_P1.27mm
U19: LM75C; SOIC-8_3.9x4.9mm_P1.27mm
U24: SN74LVC1G14DBV; SOT-23-5_HandSoldering; not fitted
XTAL1: FC-12M 32.7680KA-A0; CRYSTAL_FC-12M_EPS-M

Connections:
+3.3V: C63.2, C64.2, C67.2, C69.2, C96.2, D1.2 (A), J11.14 (+LV), J16.P6, J16.P13, J16.S7, R36.1, R37.1, R38.1, R39.1, R40.1, R41.1, R42.1, R43.1, R44.2, R45.1, R58.2, R59.2, R75.1, R79.1, R83.1, R85.1, R86.1, U13.1 (CPVDD), U13.8 (AVDD), U13.20 (DVDD), U14.10 (OE), U14.19 (V_{CCB}), U16.8 (VCC), U19.8 (+Vs)
+5V: C66.1, C68.1, J9.11 (+5V), J9.51 (+5V), J9.91 (+5V), J11.16 (+HV), J11.18 (+HV), J13.14 (+5V), J16.S1, M1.2 (+), U14.2 (V_{CCA})
AUDIO.L: C65.2, J12.3, R34.1
AUDIO.R: C70.1, J12.2, R35.1
DDR.+2.5V: C74.1, C75.1, C76.1, C77.1, C78.1, C79.1, C80.1, C81.1, C82.1, C83.1, C84.1, C85.1, C86.1, C87.1, C88.1, C89.1, C90.2, C91.1, C92.1, C93.1, C97.1, C98.1, C99.1, C100.1, C101.1, C102.1, C103.1, C104.1, C105.1, C106.1, C107.1, C108.1, C109.1, C110.1, C111.1, C112.1, J14.9 (V_{DD}), J14.10 (V_{DD}), J14.21 (V_{DD}), J14.22 (V_{DD}), J14.33 (V_{DD}), J14.34 (V_{DD}), J14.36 (V_{DD}), J14.45 (V_{DD}), J14.46 (V_{DD}), J14.57 (V_{DD}), J14.58 (V_{DD}), J14.69 (V_{DD}), J14.70 (V_{DD}), J14.81 (V_{DD}), J14.82 (V_{DD}), J14.92 (V_{DD}), J14.93 (V_{DD}), J14.94 (V_{DD}), J14.95 (CKE1), J14.96 (CKE0), J14.113 (V_{DD}), J14.114 (V_{DD}), J14.131 (V_{DD}), J14.132 (V_{DD}), J14.143 (V_{DD}), J14.144 (V_{DD}), J14.155 (V_{DD}), J14.156 (V_{DD}), J14.157 (V_{DD}), J14.167 (V_{DD}), J14.168 (V_{DD}), J14.179 (V_{DD}), J14.180 (V_{DD}), J14.191 (V_{DD}), J14.192 (V_{DD}), L3.2, R56.1, R77.2, R88.2, U15.6 (VBST), U17.2 (V_{CCA}), U17.10 (OE), U18.2 (V_{CCA}), U18.10 (OE), U20.2 (V_{CCA}), U20.10 (OE), U21.2 (V_{CCA}), U21.10 (OE), U22.2 (V_{CCA}), U22.10 (OE), U23.2 (V_{CCA}), U23.10 (OE)
DDR.+3.3V: J9.29 (+3.3V), J9.69 (+3.3V), J9.109 (+3.3V), J14.194 (SA0), J14.197 (V_{DDSPD}), JP22.1 (A), U17.19 (V_{CCB}), U18.19 (V_{CCB}), U20.19 (V_{CCB}), U21.19 (V_{CCB}), U22.19 (V_{CCB}), U23.19 (V_{CCB}), U24.5 (VCC)
DDR.A0: J14.112 (A0), U22.3 (A2)
DDR.A1: J14.111 (A1), U17.5 (A4)
DDR.A2: J14.110 (A2), U22.1 (A1)
DDR.A3: J14.109 (A3), U17.4 (A3)
DDR.A4: J14.108 (A4), U20.9 (A8)
DDR.A5: J14.107 (A5), U17.3 (A2)
DDR.A6: J14.106 (A6), U20.8 (A7)
DDR.A7: J14.105 (A7), U17.1 (A1)
DDR.A8: J14.102 (A8), U20.7 (A6)
DDR.A9: J14.101 (A9), U23.9 (A8)
DDR.A10: J14.115 (A10), U17.6 (A5)
DDR.A11: J14.100 (A11), U20.5 (A4)
DDR.A12: J14.99 (A12), U20.6 (A5)
DDR.BA0: J14.117 (BA0), U17.7 (A6)
DDR.BA1: J14.116 (BA1), U22.4 (A3)
DDR.CK0: J14.35 (CK0), U23.4 (A3)
DDR.CK1: J14.160 (CK1), U22.8 (A7)
DDR.DM0: J14.12 (DM0), U18.4 (A3)
DDR.DM1: J14.26 (DM1), U18.9 (A8)
DDR.DM2: J14.48 (DM2), U20.4 (A3)
DDR.DM3: J14.62 (DM3), U23.8 (A7)
DDR.DQ0: J14.5 (DQ0), U21.1 (A1)
DDR.DQ1: J14.7 (DQ1), U21.3 (A2)
DDR.DQ2: J14.13 (DQ2), U21.5 (A4)
DDR.DQ3: J14.17 (DQ3), U21.6 (A5)
DDR.DQ4: J14.6 (DQ4), U18.1 (A1)
DDR.DQ5: J14.8 (DQ5), U18.3 (A2)
DDR.DQ6: J14.14 (DQ6), U18.5 (A4)
DDR.DQ7: J14.18 (DQ7), U18.6 (A5)
DDR.DQ8: J14.19 (DQ8), U21.7 (A6)
DDR.DQ9: J14.23 (DQ9), U21.8 (A7)
DDR.DQ10: J14.29 (DQ10), U23.1 (A1)
DDR.DQ11: J14.31 (DQ11), U23.3 (A2)
DDR.DQ12: J14.20 (DQ12), U18.7 (A6)
DDR.DQ13: J14.24 (DQ13), U18.8 (A7)
DDR.DQ14: J14.30 (DQ14), U20.1 (A1)
DDR.DQ15: J14.32 (DQ15), U20.3 (A2)
DDR.DQS0: J14.11 (DQS0), U21.4 (A3)
DDR.DQS1: J14.25 (DQS1), U21.9 (A8)
DDR.DQS2: J14.47 (DSQ2), U23.6 (A5)
DDR.DQS3: J14.61 (DQS3), U23.7 (A6)
DDR.PG: R57.1
DDR.~CAS: J14.120 (~CAS), U22.6 (A5)
DDR.~CK0: J14.37 (~CK0), U23.5 (A4)
DDR.~CK1: J14.158 (~CK1), U22.9 (A8)
DDR.~RAS: J14.118 (~RAS), U22.5 (A4)
DDR.~S0: J14.121 (~S0), U17.9 (A8)
DDR.~S1: J14.122 (~S1), U22.7 (A6)
DDR.~WE: J14.119 (~WE), U17.8 (A7)
DDR_+3V3.A0: J9.77 (GPIO_0_D32), U22.18 (B2)
DDR_+3V3.A1: J9.78 (GPIO_0_D33), U17.16 (B4)
DDR_+3V3.A2: J9.79 (GPIO_0_D34), U22.20 (B1)
DDR_+3V3.A3: J9.80 (GPIO_0_D35), U17.17 (B3)
DDR_+3V3.A4: J9.68 (GPIO_0_D25), U20.12 (B8)
DDR_+3V3.A5: J9.65 (GPIO_0_D22), U17.18 (B2)
DDR_+3V3.A6: J9.66 (GPIO_0_D23), U20.13 (B7)
DDR_+3V3.A7: J9.63 (GPIO_0_D20), U17.20 (B1)
DDR_+3V3.A8: J9.64 (GPIO_0_D21), U20.14 (B6)
DDR_+3V3.A9: J9.61 (GPIO_0_D18), U23.12 (B8)
DDR_+3V3.A10: J9.76 (GPIO_0_D31), U17.15 (B5)
DDR_+3V3.A11: J9.62 (GPIO_0_D19), U20.16 (B4)
DDR_+3V3.A12: J9.59 (GPIO_0_D16), U20.15 (B5)
DDR_+3V3.BA0: J9.74 (GPIO_0_D29), U17.14 (B6)
DDR_+3V3.BA1: J9.75 (GPIO_0_D30), U22.17 (B3)
DDR_+3V3.CK0: J9.60 (GPIO_0_D17), U23.17 (B3), U24.2
DDR_+3V3.CK1: J9.114 (GPIO_1_D29), U22.13 (B7)
DDR_+3V3.DM0: J9.118 (GPIO_1_D33), U18.17 (B3)
DDR_+3V3.DM1: J9.117 (GPIO_1_D32), U18.12 (B8)
DDR_+3V3.DM2: J9.120 (GPIO_1_D35), U20.17 (B3)
DDR_+3V3.DM3: J9.115 (GPIO_1_D30), U23.13 (B7)
DDR_+3V3.DQ0: J9.41 (GPIO_0_D0), U21.20 (B1)
DDR_+3V3.DQ1: J9.42 (GPIO_0_D1), U21.18 (B2)
DDR_+3V3.DQ2: J9.43 (GPIO_0_D2), U21.16 (B4)
DDR_+3V3.DQ3: J9.44 (GPIO_0_D3), U21.15 (B5)
DDR_+3V3.DQ4: J9.45 (GPIO_0_D4), U18.20 (B1)
DDR_+3V3.DQ5: J9.46 (GPIO_0_D5), U18.18 (B2)
DDR_+3V3.DQ6: J9.47 (GPIO_0_D6), U18.16 (B4)
DDR_+3V3.DQ7: J9.48 (GPIO_0_D7), U18.15 (B5)
DDR_+3V3.DQ8: J9.58 (GPIO_0_D15), U21.14 (B6)
DDR_+3V3.DQ9: J9.57 (GPIO_0_D14), U21.13 (B7)
DDR_+3V3.DQ10: J9.56 (GPIO_0_D13), U23.20 (B1)
DDR_+3V3.DQ11: J9.55 (GPIO_0_D12), U23.18 (B2)
DDR_+3V3.DQ12: J9.54 (GPIO_0_D11), U18.14 (B6)
DDR_+3V3.DQ13: J9.53 (GPIO_0_D10), U18.13 (B7)
DDR_+3V3.DQ14: J9.49 (GPIO_0_D8), U20.20 (B1)
DDR_+3V3.DQ15: J9.50 (GPIO_0_D9), U20.18 (B2)
DDR_+3V3.DQS0: U21.17 (B3)
DDR_+3V3.DQS1: J9.119 (GPIO_1_D34), U21.12 (B8)
DDR_+3V3.DQS2: J9.116 (GPIO_1_D31), U23.15 (B5)
DDR_+3V3.DQS3: J9.107 (GPIO_1_D24), U23.14 (B6)
DDR_+3V3.~CAS: J9.71 (GPIO_0_D26), U22.15 (B5)
DDR_+3V3.~CK0: JP24.1 (A), U23.16 (B4), U24.4
DDR_+3V3.~CK1: J9.113 (GPIO_1_D28), U22.12 (B8)
DDR_+3V3.~RAS: J9.72 (GPIO_0_D27), U22.16 (B4)
DDR_+3V3.~S0: J9.73 (GPIO_0_D28), U17.12 (B8)
DDR_+3V3.~S1: J9.106 (GPIO_1_D23), U22.14 (B6)
DDR_+3V3.~WE: J9.67 (GPIO_0_D24), U17.13 (B7)
EC_FAN.PWM: R84.1
EC_FAN.SENS: R82.2
EC_I2C.SCL: J14.195 (SCL), J16.P8, U19.2 (SCL)
EC_I2C.SDA: J14.193 (SDA), J16.P7, U19.1 (SDA)
EC_TEMP.~INT: R86.2, U19.3 (O.S.)
EC_VGA.B: J13.C3 (Blue), R73.2, R74.1
EC_VGA.B0: R74.2
EC_VGA.B1: R73.1
EC_VGA.G: J13.C2 (Green), R71.1, R72.2
EC_VGA.G0: R72.1
EC_VGA.G1: R71.2
EC_VGA.HSYNC: R76.1
EC_VGA.R: J13.C1 (Red), R67.1, R68.2
EC_VGA.R0: R68.1
EC_VGA.R1: R67.2
EC_VGA.VSYNC: R78.1
EN: R57.2, U15.5 (EN)
EXP_CCD.D+: J16.S5
EXP_CCD.D-: J16.S6
EXP_EC.ADC: J16.P9
EXP_FPGA_IO.B61N: J9.112 (GPIO_1_D27), J16.P12
EXP_FPGA_IO.B61P: J9.111 (GPIO_1_D26), J16.P11
EXP_FPGA_IO.B66N: J9.108 (GPIO_1_D25), J16.P15
EXP_FPGA_IO.B66P: J9.105 (GPIO_1_D22), J16.P14
EXP_OTG.D+: J16.S2
EXP_OTG.D-: J16.S3
Earth: J11.SH, J13.SH, JP21.1 (A), JP23.1 (A)
FPGA.SCL: J9.19 (Arduino_IO4), J13.6 (DDCCL), J16.P2, R59.1, U16.6 (SCL)
FPGA.SDA: J9.10 (Arduino_IO3), J13.7 (DDCIO), J16.P1, R58.1, U16.5 (SDA)
FPGA_BTN.OSD: J9.18 (Arduino_IO1), R83.2, SW2.OSD1.1
FPGA_BTN.RST: J9.14 (Arduino_IO0), R75.2, SW1.RST1.1
FPGA_BTN.USR: J9.17 (Arduino_IO5), R85.2, SW3.USR1.1
FPGA_DP.AUX+: J9.87 (GPIO_1_D6)
FPGA_DP.AUX-: J9.84 (GPIO_1_D3)
FPGA_DP.DP0+: J9.81 (GPIO_1_D0)
FPGA_DP.DP0-: J9.83 (GPIO_1_D2)
FPGA_DP.DP1+: J9.88 (GPIO_1_D7)
FPGA_DP.DP1-: J9.86 (GPIO_1_D5)
FPGA_DP.DP2+: J9.85 (GPIO_1_D4)
FPGA_DP.DP2-: J9.90 (GPIO_1_D9)
FPGA_DP.HPD: J9.82 (GPIO_1_D1)
FPGA_DP.~LP: J9.89 (GPIO_1_D8)
FPGA_DVI.CK+: J9.103 (GPIO_1_D20), R69.2
FPGA_DVI.CK-: J9.100 (GPIO_1_D17), R70.2
FPGA_DVI.D0+: J9.93 (GPIO_1_D10), R65.2
FPGA_DVI.D0-: J9.96 (GPIO_1_D13), R66.2
FPGA_DVI.D1+: J9.95 (GPIO_1_D12), R63.2
FPGA_DVI.D1-: J9.99 (GPIO_1_D16), R64.2
FPGA_DVI.D2+: J9.97 (GPIO_1_D14), R61.2
FPGA_DVI.D2-: J9.98 (GPIO_1_D15), R62.2
FPGA_DVI.HPD: J9.102 (GPIO_1_D19), R80.2
FPGA_EXP_HPS.SCL: J9.40 (HPS_I2C1_SCLK), J16.P4
FPGA_EXP_HPS.SDA: J9.39 (HPS_I2C1_SDAT), J16.P5
FPGA_I2S.BCK: J9.9 (Arduino_IO2), U13.13 (BCK)
FPGA_I2S.DIN: J9.5 (ADC_SDI), U13.14 (DIN)
FPGA_I2S.LRCK: J9.7 (Arduino_IO6), U13.15 (LRCK)
FPGA_I2S.~MUTE: J9.8 (Arduino_IO7), Q3.2 (E)
FPGA_LED.DSK: J9.26 (LED6), R90.2
FPGA_LED.PWR: J9.31 (LED7), R87.2
FPGA_LED.USR: J9.32 (LED5), R89.2
FPGA_SNAC.IO0: J9.3 (Arduino_IO14), R36.2, U14.20 (B1)
FPGA_SNAC.IO1: J9.13 (Arduino_IO15), R37.2, U14.18 (B2)
FPGA_SNAC.IO2: J9.20 (Arduino_IO10), R38.2, U14.17 (B3)
FPGA_SNAC.IO3: J9.2 (Arduino_IO12), R39.2, U14.16 (B4)
FPGA_SNAC.IO4: J9.1 (Arduino_IO13), R40.2, U14.15 (B5)
FPGA_SNAC.IO5: J9.21 (Arduino_IO11), R41.2, U14.14 (B6)
FPGA_SNAC.IO6: J9.23 (Arduino_IO8), R42.2, U14.13 (B7)
FPGA_SNAC.IO7: J9.4 (ADC_SDO), R43.2, U14.12 (B8)
FPGA_SNAC_HPS.CLK: J9.35 (HPS_SPIM_CLK), J11.10 (LV_{IO}1)
FPGA_SNAC_HPS.MISO: J9.36 (HPS_SPIM_MISO), J11.12 (LV_{IO}3)
FPGA_SNAC_HPS.MOSI: J9.33 (HPS_SPIM_MOSI), J11.9 (LV_{IO}0)
FPGA_SNAC_HPS.S: J9.34 (HPS_SPIM_SS), J11.11 (LV_{IO}2)
FPGA_SNAC_HPS.SCL: J9.38 (HPS_I2C0_SCLK), J11.17 (LV_{IO}5)
FPGA_SNAC_HPS.SDA: J9.37 (HPS_I2C0_SDAT), J11.13 (LV_{IO}4)
FPGA_UART.RXD: J9.15 (ADC_CONVST)
FPGA_UART.TXD: J9.16 (ADC_SCK)
GND: BT1.N, C63.1, C64.1, C65.1, C66.2, C67.1, C68.2, C69.1, C70.2, C72.2, C73.2, C74.2, C75.2, C76.2, C77.2, C78.2, C79.2, C80.2, C81.2, C82.2, C83.2, C84.2, C85.2, C86.2, C87.2, C88.2, C89.2, C91.2, C92.2, C93.2, C94.2, C95.2, C96.1, C97.2, C98.2, C99.2, C100.2, C101.2, C102.2, C103.2, C104.2, C105.2, C106.2, C107.2, C108.2, C109.2, C110.2, C111.2, C112.2, C113.1, C114.1, J9.12 (GND), J9.30 (GND), J9.52 (GND), J9.70 (GND), J9.92 (GND), J9.110 (GND), J11.15 (GND), J11.19 (GND), J12.1, J13.3 (D2/4S), J13.11 (D1/3S), J13.15 (GND), J13.19 (D0/5S), J13.22 (CKS), J13.C5 (GNDA), J14.3 (V_{SS}), J14.4 (V_{SS}), J14.15 (V_{SS}), J14.16 (V_{SS}), J14.27 (V_{SS}), J14.28 (V_{SS}), J14.38 (V_{SS}), J14.39 (V_{SS}), J14.40 (V_{SS}), J14.51 (V_{SS}), J14.52 (V_{SS}), J14.63 (V_{SS}), J14.64 (V_{SS}), J14.75 (V_{SS}), J14.76 (V_{SS}), J14.87 (V_{SS}), J14.88 (V_{SS}), J14.90 (V_{SS}), J14.103 (V_{SS}), J14.104 (V_{SS}), J14.125 (V_{SS}), J14.126 (V_{SS}), J14.137 (V_{SS}), J14.138 (V_{SS}), J14.149 (V_{SS}), J14.150 (V_{SS}), J14.159 (V_{SS}), J14.161 (V_{SS}), J14.162 (V_{SS}), J14.173 (V_{SS}), J14.174 (V_{SS}), J14.185 (V_{SS}), J14.186 (V_{SS}), J14.198 (SA2), J14.200 (V_{SS}), J15.5, J16.P3, J16.P10, J16.S4, J16.SH1 (SHIELD), J16.SH2 (SHIELD__1), JP20.1 (A), JP21.2 (B), JP22.3 (B), JP23.2 (B), M1.1 (-), R44.1, R52.1, R60.1, R81.1, R88.1, SW1.RST1.2, SW1.RST1.3, SW1.RST1.4, SW2.OSD1.2, SW2.OSD1.3, SW2.OSD1.4, SW3.USR1.2, SW3.USR1.3, SW3.USR1.4, U13.3 (CPGND), U13.9 (AGND), U13.10 (DEMP), U13.12 (SCK), U13.16 (FMT), U13.19 (DGND), U14.11 (GND), U15.1 (GND), U16.4 (VSS), U17.11 (GND), U18.11 (GND), U19.4 (GND), U19.5 (A2), U19.6 (A1), U19.7 (A0), U20.11 (GND), U21.11 (GND), U22.11 (GND), U23.11 (GND), U24.3 (GND)
I2S_FLT: JP20.2 (B), R45.2, U13.11 (FLT)
unnamed: C71.1, U13.2 (CAPP)
unnamed: C71.2, U13.4 (CAPM)
unnamed: C72.1, U13.5 (VNEG)
unnamed: C73.1, U13.18 (LDOO)
unnamed: C113.2, M1.3 (Tacho), R79.2, R82.1
unnamed: C114.2, M1.4 (PWM), R84.2
unnamed: D1.1 (K), R91.2
unnamed: J9.104 (GPIO_1_D21), JP24.2 (B)
unnamed: J13.1 (D2-), R62.1
unnamed: J13.2 (D2+), R61.1
unnamed: J13.8 (VSYNC), R78.2
unnamed: J13.9 (D1-), R64.1
unnamed: J13.10 (D1+), R63.1
unnamed: J13.16 (HPD), R80.1
unnamed: J13.17 (D0-), R66.1
unnamed: J13.18 (D0+), R65.1
unnamed: J13.23 (CK+), R69.1
unnamed: J13.24 (CK-), R70.1
unnamed: J13.C4 (HSYNC), R76.2
unnamed: J14.1 (V_{REF}), J14.2 (V_{REF}), R77.1, R81.2
unnamed: J14.85 (NC), J14.86 (NC), J14.97 (NC), J14.98 (NC), J14.123 (NC), J14.124 (NC), J14.199 (NC)
unnamed: J14.196 (SA1), JP22.2 (C)
unnamed: J15.1, R87.1
unnamed: J15.2, R89.1
unnamed: J15.3, R90.1
unnamed: Q3.1 (B), R55.1
unnamed: Q3.3 (C), R52.2, U13.17 (XSMT)
unnamed: R34.2, U13.6 (OUTL)
unnamed: R35.2, U13.7 (OUTR)
unnamed: R46.2, U14.1 (A1)
unnamed: R47.2, U14.3 (A2)
unnamed: R48.2, U14.4 (A3)
unnamed: R49.2, U14.5 (A4)
unnamed: R50.2, U14.6 (A5)
unnamed: R51.2, U14.7 (A6)
unnamed: R53.2, U14.8 (A7)
unnamed: R54.2, U14.9 (A8)
RTC.VBAT: BT1.P, U16.3 (VBAT)
RTC.X1: U16.1 (X1), XTAL1.2
RTC.X2: U16.2 (X2), XTAL1.1
SNAC.IO0: J11.1 (HV_{IO}0), R46.1
SNAC.IO1: J11.2 (HV_{IO}1), R47.1
SNAC.IO2: J11.3 (HV_{IO}2), R48.1
SNAC.IO3: J11.4 (HV_{IO}3), R49.1
SNAC.IO4: J11.5 (HV_{IO}4), R50.1
SNAC.IO5: J11.6 (HV_{IO}5), R51.1
SNAC.IO6: J11.7 (HV_{IO}6), R53.1
SNAC.IO7: J11.8 (HV_{IO}7), R54.1
SW: C90.1, L3.1, U15.2 (SW)
USBC_VBUS: C94.1, C95.1, R55.2, U15.3 (VIN)
VFB: R56.2, R60.2, U15.4 (VFB)
~Ard_RST: J9.6 (~Arduino_Reset), R91.1

Notes on the sheet:
DDR SODIMM
KBD LED
!!!! NOTE: DNI all DDR SODIMM for !!!! QMTECH_Cyclone_V_SoC_KFB_With_Dual_SDRAM
PCB: Place close to cutout
PCB: Mount on the Left Side PCMIA port
RESET
SNAC_{HDMI}
DVI-D DVI-A (EC)
USER
2.5V SWR
QMTECH_Cyclone_V_SoC_KFB
LINE OUT
OSD
R^{2}G^{2}B^{2}
CORE OSD
FLT Pin Interpolation Filters H: IIR Low Latency (Default) L: FIR Normal Interpolation Filters
LED Connector
open hardware
I2C Address = 0x48
FPGA FAN
I2C Address: 0bxxxx011
Internal Expansion Port
Inter-sheet connections
RTC
!! DDR SDRAM = ~2W !! Activate after EC determines supply has enough power
V_{out}=0.6 x ( 1+ R_{VBST-VFB} / R_{VFB-GND} )
LPF
